desvandi/PLTSMonitoring_Firmware-Backend/firmware/Drivers/RtcDriver.cpp

// =============================================================================
// Drivers/RtcDriver.cpp — DS3231 RTC + NTP fallback
// =============================================================================
#include "RtcDriver.h"
#include "../Core/Config.h"
#include <Wire.h>
#include <time.h>

namespace Drivers {

RtcDriver rtc;

bool RtcDriver::_ds3231Read(uint8_t reg, uint8_t& out) {
  Wire.beginTransmission(0x68);
  Wire.write(reg);
  if (Wire.endTransmission(false) != 0) return false;
  if (Wire.requestFrom(0x68, 1) != 1) return false;
  out = Wire.read();
  return true;
}

bool RtcDriver::_ds3231Write(uint8_t reg, uint8_t val) {
  Wire.beginTransmission(0x68);
  Wire.write(reg);
  Wire.write(val);
  return Wire.endTransmission() == 0;
}

static uint8_t bcd2dec(uint8_t b) { return (b >> 4) * 10 + (b & 0x0F); }
static uint8_t dec2bcd(uint8_t d) { return ((d / 10) << 4) | (d % 10); }

bool RtcDriver::_ds3231GetTime(struct tm& t) {
  uint8_t sec, min, hr, wd, day, mon, yr;
  if (!_ds3231Read(0x00, sec) || !_ds3231Read(0x01, min) ||
      !_ds3231Read(0x02, hr)  || !_ds3231Read(0x03, wd) ||
      !_ds3231Read(0x04, day) || !_ds3231Read(0x05, mon) ||
      !_ds3231Read(0x06, yr)) return false;
  t.tm_sec  = bcd2dec(sec & 0x7F);
  t.tm_min  = bcd2dec(min);
  t.tm_hour = bcd2dec(hr & 0x3F);
  t.tm_wday = bcd2dec(wd) - 1;
  t.tm_mday = bcd2dec(day);
  t.tm_mon  = bcd2dec(mon & 0x1F) - 1;
  t.tm_year = bcd2dec(yr) + 100;  // 2000 + yr - 1900
  return true;
}
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
